ausprecision/Target-Camera-ESP32-CAM/Arduino/ESP32-CAM-Version-7/camera_index.h

//File: index_ov2640.html.gz, Size: 6787
#define index_ov2640_html_gz_len 6787
const uint8_t index_ov2640_html_gz[] = {
  0x1F, 0x8B, 0x08, 0x08, 0x23, 0xFC, 0x69, 0x5E, 0x00, 0x03, 0x69, 0x6E, 0x64, 0x65, 0x78, 0x5F, 0x6F, 0x76, 0x32, 0x36, 0x34, 0x30, 0x2E, 0x68, 0x74, 0x6D,
  0x6C, 0x00, 0xED, 0x3D, 0x6B, 0x73, 0xDB, 0x46, 0x92, 0xDF, 0xFD, 0x2B, 0x60, 0x24, 0x6B, 0x92, 0x25, 0x92, 0x22, 0x29, 0x4A, 0x96, 0x15, 0x89, 0x3E, 0x5B,
  0x96, 0x1F, 0xB5, 0x76, 0xE2, 0xB5, 0x12, 0xC7, 0x5B, 0xA9, 0x2D, 0x07, 0x04, 0x86, 0x24, 0x62, 0x10, 0xE0, 0x02, 0xA0, 0x48, 0x26, 0xA5, 0xDF, 0x71, 0x3F,
  0xE8, 0xFE, 0xD8, 0x75, 0xCF, 0x03, 0x18, 0x00, 0x83, 0x07, 0x49, 0x89, 0xF4, 0xFA, 0x8E, 0x4E, 0x45, 0x78, 0x4C, 0xF7, 0xF4, 0xBB, 0x7B, 0x66, 0x30, 0xC0,
  0xF9, 0x43, 0xCB, 0x33, 0xC3, 0xD5, 0x8C, 0x68, 0x93, 0x70, 0xEA, 0x0C, 0x1E, 0x9C, 0xB3, 0x3F, 0x1A, 0xFC, 0xCE, 0x27, 0xC4, 0xB0, 0xD8, 0x21, 0x3D, 0x9D,
  0x92, 0xD0, 0xD0, 0xCC, 0x89, 0xE1, 0x07, 0x24, 0xBC, 0xD0, 0xE7, 0xE1, 0xA8, 0x75, 0xAA, 0xA7, 0x6F, 0xBB, 0xC6, 0x94, 0x5C, 0xE8, 0x37, 0x36, 0x59, 0xCC,
  0x3C, 0x3F, 0xD4, 0x35, 0xD3, 0x73, 0x43, 0xE2, 0x42, 0xF3, 0x85, 0x6D, 0x85, 0x93, 0x0B, 0x8B, 0xDC, 0xD8, 0x26, 0x69, 0xD1, 0x93, 0xA6, 0xED, 0xDA, 0xA1,
  0x6D, 0x38, 0xAD, 0xC0, 0x34, 0x1C, 0x72, 0xD1, 0x95, 0x71, 0x85, 0x76, 0xE8, 0x90, 0xC1, 0xD5, 0xF5, 0xFB, 0xA3, 0x9E, 0xF6, 0xD3, 0xC7, 0x5E, 0xFF, 0xA4,
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
  0xC5, 0x03, 0x11, 0x16, 0x10, 0x9A, 0x5A, 0x9B, 0x1D, 0x6C, 0x50, 0x95, 0x48, 0xFA, 0x2D, 0x24, 0xA4, 0xAB, 0xB4, 0x0E, 0x56, 0x98, 0x28, 0x3D, 0x27, 0x69,
  0x5B, 0xCA, 0x42, 0xBF, 0x34, 0x34, 0x88, 0x21, 0xDF, 0x68, 0x54, 0x36, 0x68, 0x1C, 0x8D, 0x8E, 0x3A, 0x47, 0xFD, 0xD2, 0xCA, 0x49, 0xC9, 0x65, 0x6A, 0xE0,
  0xA8, 0x08, 0x1D, 0x51, 0x58, 0x29, 0x34, 0x82, 0xC0, 0xB8, 0x51, 0x16, 0xED, 0x5E, 0x60, 0xB3, 0x91, 0x9B, 0x31, 0x0C, 0x60, 0xEC, 0x16, 0x2A, 0x86, 0x5E,
  0xDC, 0xD0, 0x7B, 0x4A, 0xFA, 0x68, 0x49, 0xA7, 0x74, 0x01, 0x21, 0x5E, 0x35, 0xD9, 0x09, 0x0D, 0xA8, 0x9B, 0x48, 0x0A, 0x56, 0x16, 0x95, 0x21, 0x59, 0x86,
  0x2D, 0x8B, 0x98, 0x9E, 0xCF, 0xAA, 0xC1, 0x9C, 0x91, 0x63, 0x4A, 0x91, 0xE5, 0x16, 0x7B, 0x36, 0xF1, 0x6E, 0x88, 0xAF, 0x10, 0x56, 0x4A, 0xA9, 0xFD, 0x27,
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
};
